impatrq/AgroNomad/firmware/AgroBot/server/db/dbs/image.png

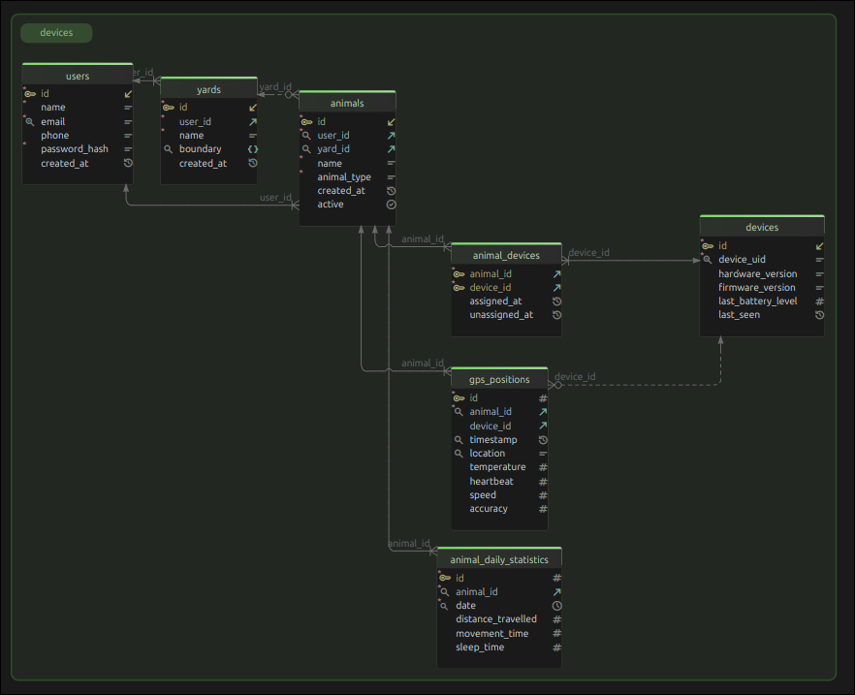
firmware/AgroBot/server/db/dbs/image.png
