impatrq/AgroNomad/hardware/AgroBot/AgroBotPCB.png

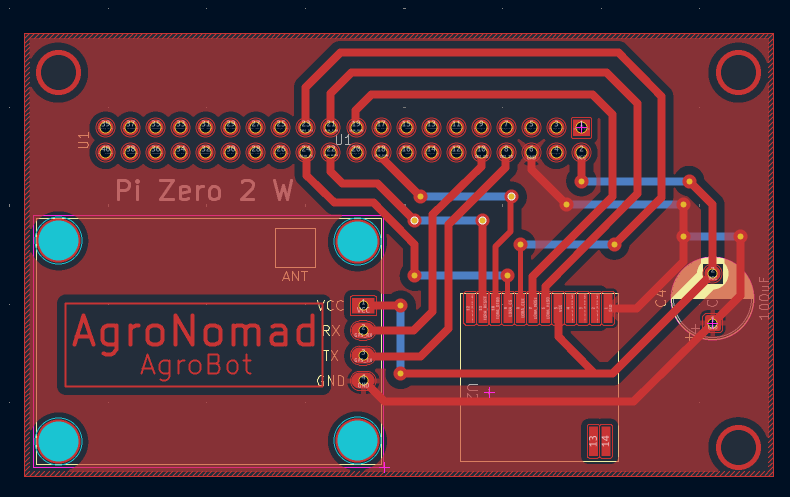
hardware/AgroBot/AgroBotPCB.png
