impatrq/AgroNomad/hardware/Solaria/SolariaPCB.png

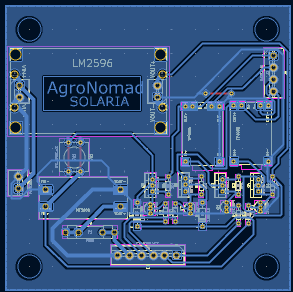
hardware/Solaria/SolariaPCB.png
