impatrq/AgroNomad/web/src/assets/agronomad/Images/cowfield.png

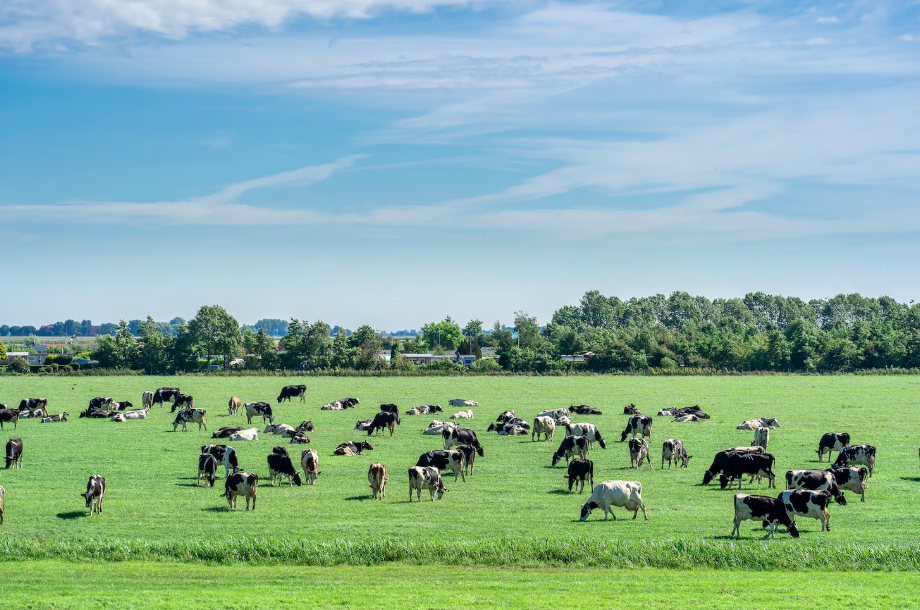
web/src/assets/agronomad/Images/cowfield.png
