impatrq/AgroNomad/web/src/assets/agronomad/Images/greenField.jpg

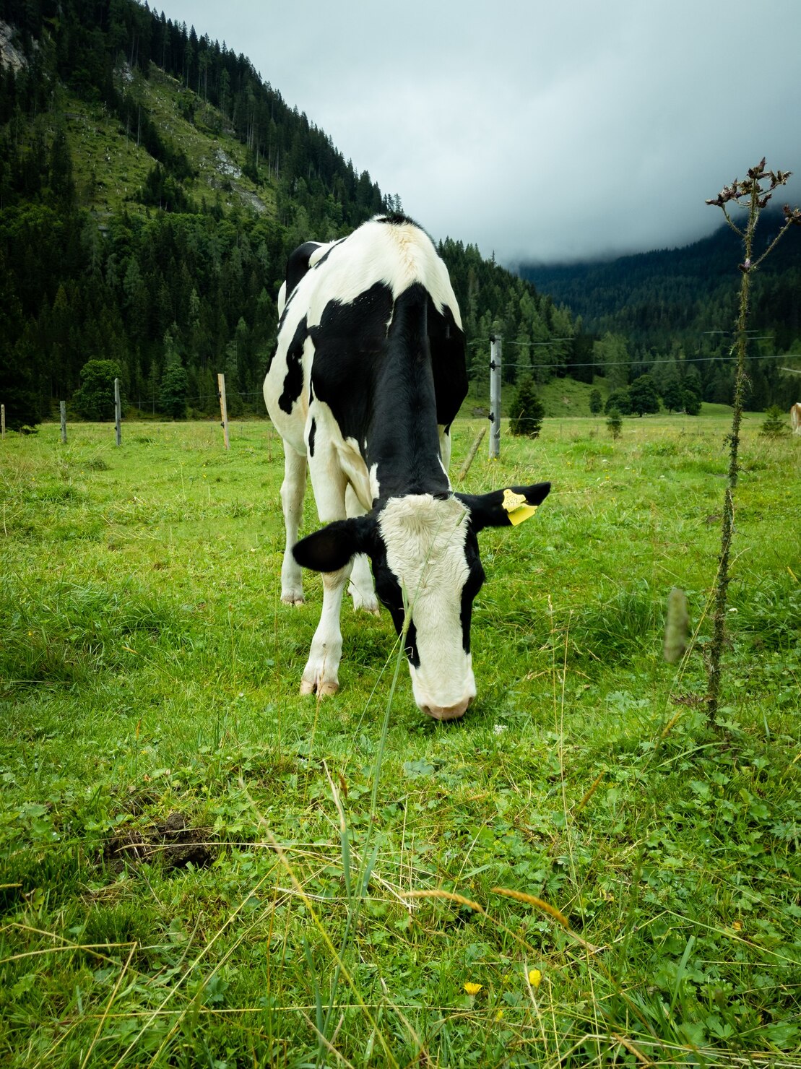
web/src/assets/agronomad/Images/greenField.jpg
