impatrq/AgroNomad/web/src/assets/agronomad/Presentation1/NomadC1S1.jpeg

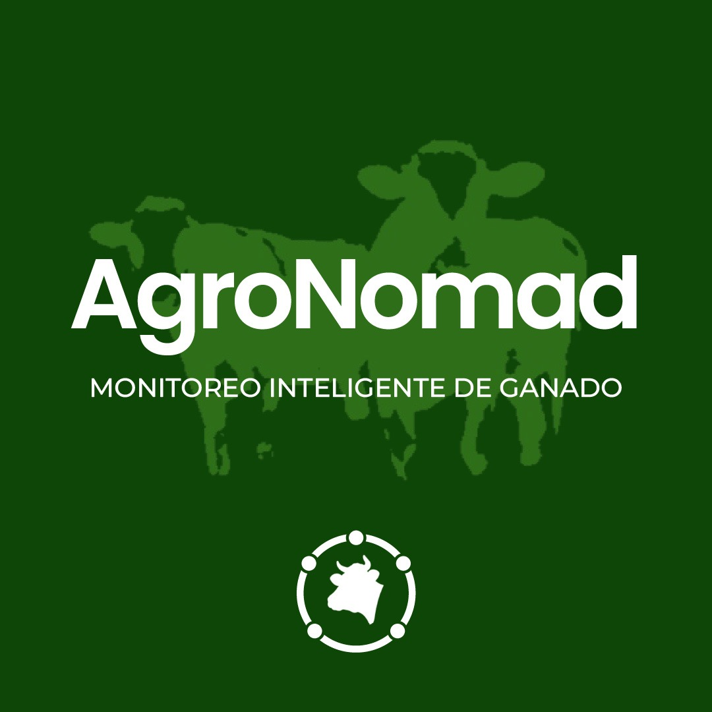
web/src/assets/agronomad/Presentation1/NomadC1S1.jpeg
