impatrq/AgroNomad/web/src/assets/agronomad/Presentation1/NomadC1S2.jpeg

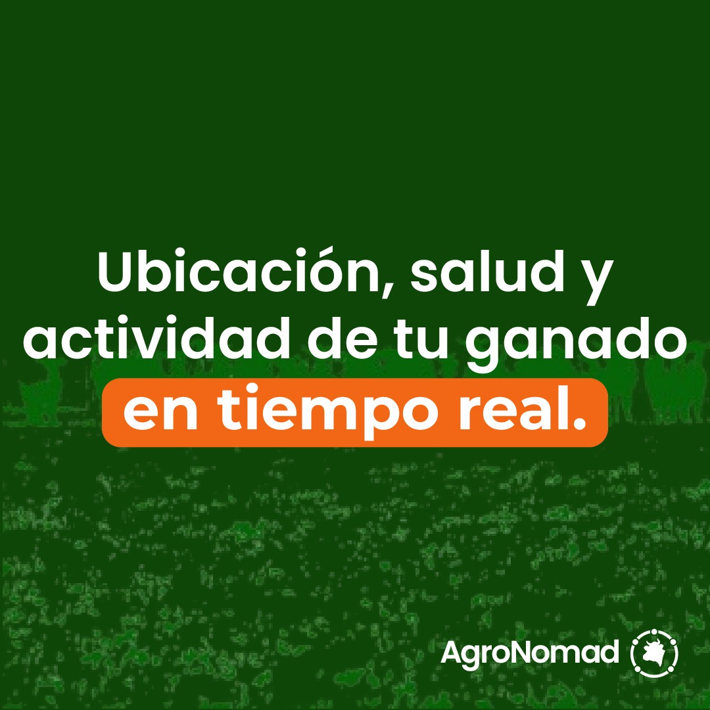
web/src/assets/agronomad/Presentation1/NomadC1S2.jpeg
