impatrq/AgroNomad/web/src/assets/agronomad/Presentation1/NomadC1S3.jpeg

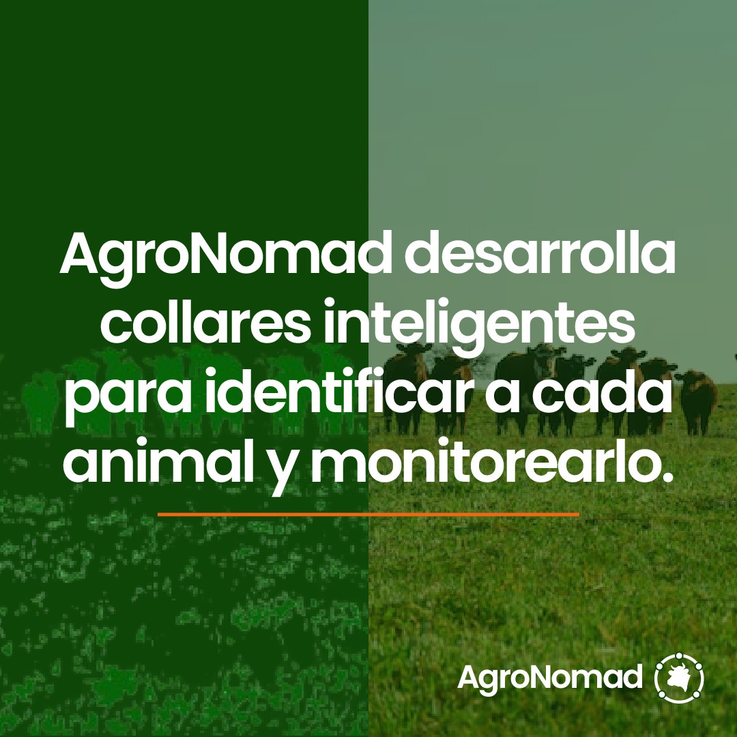
web/src/assets/agronomad/Presentation1/NomadC1S3.jpeg
