impatrq/AgroNomad/web/src/assets/agronomad/Presentation1/NomadC1S4.jpeg

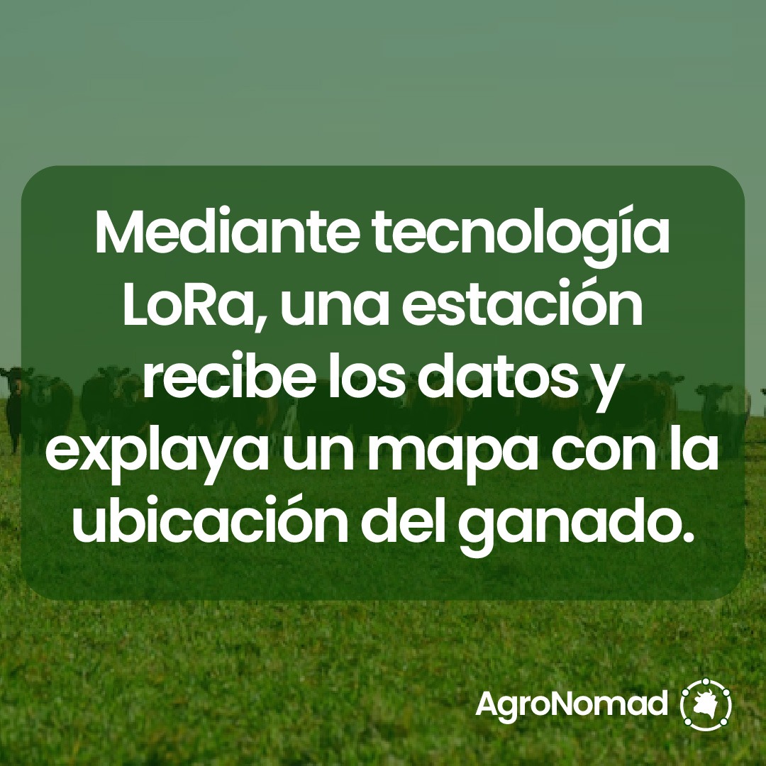
web/src/assets/agronomad/Presentation1/NomadC1S4.jpeg
