impatrq/AgroNomad/web/src/assets/agronomad/Presentation2/NomadC2S1.jpeg

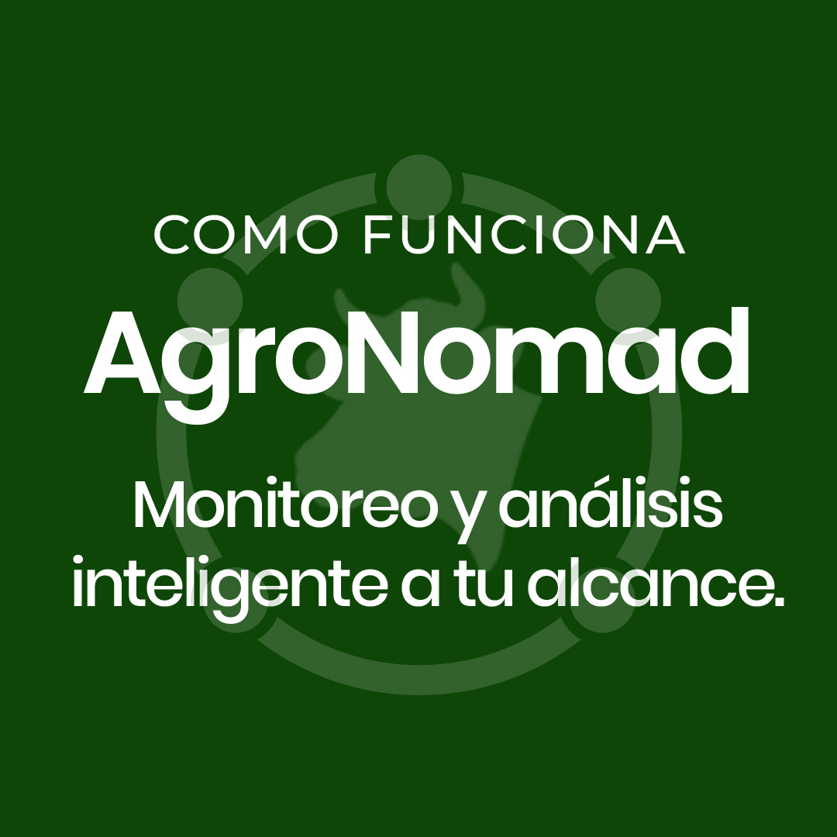
web/src/assets/agronomad/Presentation2/NomadC2S1.jpeg
