impatrq/AgroNomad/web/src/assets/agronomad/Presentation2/NomadC2S2.jpeg

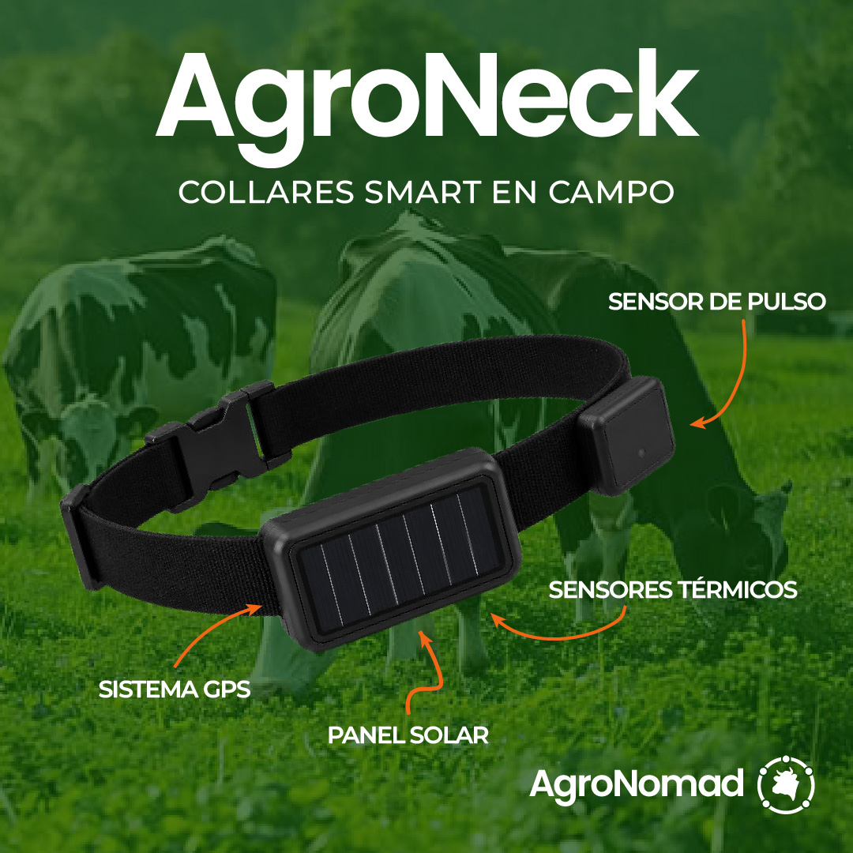
web/src/assets/agronomad/Presentation2/NomadC2S2.jpeg
