impatrq/AgroNomad/web/src/assets/agronomad/Presentation2/NomadC2S3.jpeg

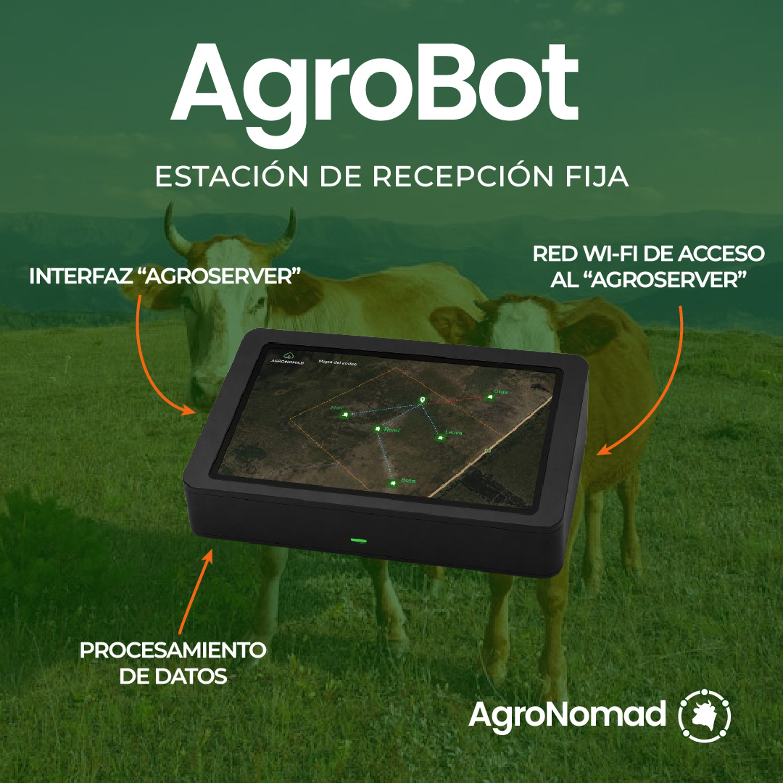
web/src/assets/agronomad/Presentation2/NomadC2S3.jpeg
