impatrq/AgroNomad/web/src/assets/agronomad/Presentation2/NomadC2S4.jpeg

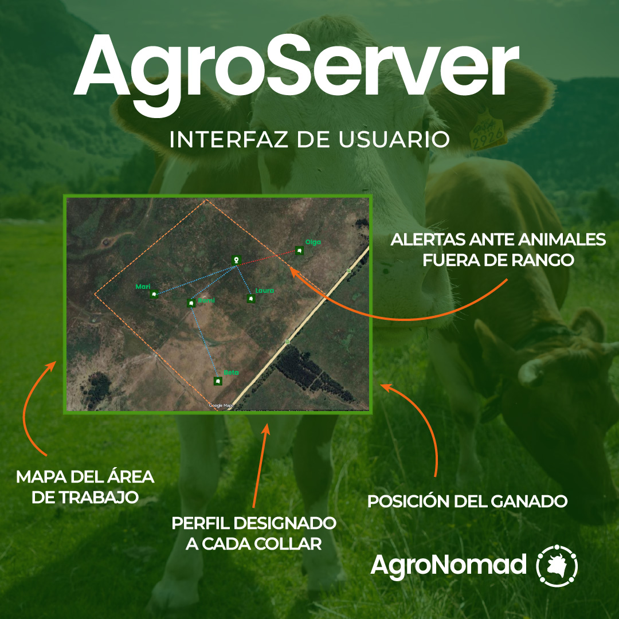
web/src/assets/agronomad/Presentation2/NomadC2S4.jpeg
