impatrq/AgroNomad/firmware/AgroNeck/components/mpumlx/mpumlx.h

#include <stdint.h>
#include <stddef.h>
#include "driver/i2c.h"
#include "esp_err.h"
 
// Pines MPU/MLX
#define MLX_MPU6050_SDA          21 // GPIO para SDA del MPU6050 y del MLX90614
#define MLX_MPU6050_SCL          22 // GPIO para SCL del MPU6050 y del MLX90614
#define MPU6050_INT              27

// Config I2C/REGS
#define MLX90614_I2C_ADDR        0x5A
#define MPU6050_I2C_ADDR         0x68
#define MPU6050_WHO_AM_I_REG     0x75
#define MPU6050_PWR_MGMT_1_REG   0x6B
#define MPU6050_PWR_MGMT_2_REG   0x6C
#define MPU6050_ACCEL_XOUT_H     0x3B
#define MPU6050_GYRO_XOUT_H      0x43
#define MPU6050_ACCEL_CONFIG     0x1C
#define MPU6050_MOT_THR          0x1F
#define MPU6050_MOT_DUR          0x20
#define MPU6050_INT_ENABLE       0x38
#define MPU6050_INT_PIN_CFG      0x37
#define MPU6050_INT_STATUS       0x3A

// Sensibilidad media de detección
#define MPU6050_THRESHOLD 20

// Estructuras
typedef struct {
    int16_t ax;
    int16_t ay; 
    int16_t az;
    int16_t gx;
    int16_t gy;
    int16_t gz;
} mpu6050_data_t;

typedef struct {
    float mlx_amb_temp;
    float mlx_object_temp;
} mlx90614_data_t;

// Funciones
void init_i2c();
esp_err_t mpu6050_init(i2c_port_t i2c_num); // una vez funcional con los dos componentes, esto probablemente debería ir adentro del init_i2c()
esp_err_t mpu6050_read(mpu6050_data_t *data, i2c_port_t i2c_num);
esp_err_t mpu6050_enable_wom(i2c_port_t i2c_num, uint8_t threshold_val); // funcion para activar el modo Wake-On-Motion
esp_err_t mpu6050_clear_int(i2c_port_t i2c_num); // funcion para limpiar el pin INT del MPU6050
esp_err_t mlx90614_read(mlx90614_data_t *data, i2c_port_t i2c_num);
